rodolfoviolac/qser/docs/latex/main_8c.tex

\hypertarget{main_8c}{}\doxysection{src/main.c File Reference}
\label{main_8c}\index{src/main.c@{src/main.c}}

Função principal, responsável pela chamada das demais rotinas.  

{\ttfamily \#include $<$stdio.\+h$>$}\newline
{\ttfamily \#include \char`\"{}pthread.\+h\char`\"{}}\newline
{\ttfamily \#include \char`\"{}math.\+h\char`\"{}}\newline
{\ttfamily \#include \char`\"{}main\+Thread/main\+Thread.\+h\char`\"{}}\newline
\doxysubsection*{Functions}
\begin{DoxyCompactItemize}
\item 
\mbox{\Hypertarget{main_8c_ae66f6b31b5ad750f1fe042a706a4e3d4}\label{main_8c_ae66f6b31b5ad750f1fe042a706a4e3d4}} 
int \mbox{\hyperlink{main_8c_ae66f6b31b5ad750f1fe042a706a4e3d4}{main}} ()
\begin{DoxyCompactList}\small\item\em Função principal. Rotinal main responsável pela inicialização do Qser e criação das thread do usuário. \end{DoxyCompactList}\end{DoxyCompactItemize}

\doxysubsection{Detailed Description}
Função principal, responsável pela chamada das demais rotinas. 

\begin{DoxyAuthor}{Author}
Rodolfo Viola Carvalho, Gabriel Alexandre Zillmer, Felipe Fuhr Dos Reis 
\end{DoxyAuthor}
\begin{DoxyDate}{Date}
11 Dec 2019 
\end{DoxyDate}
